cschempp/robotic-assembly-benchmark/static/images/board.png

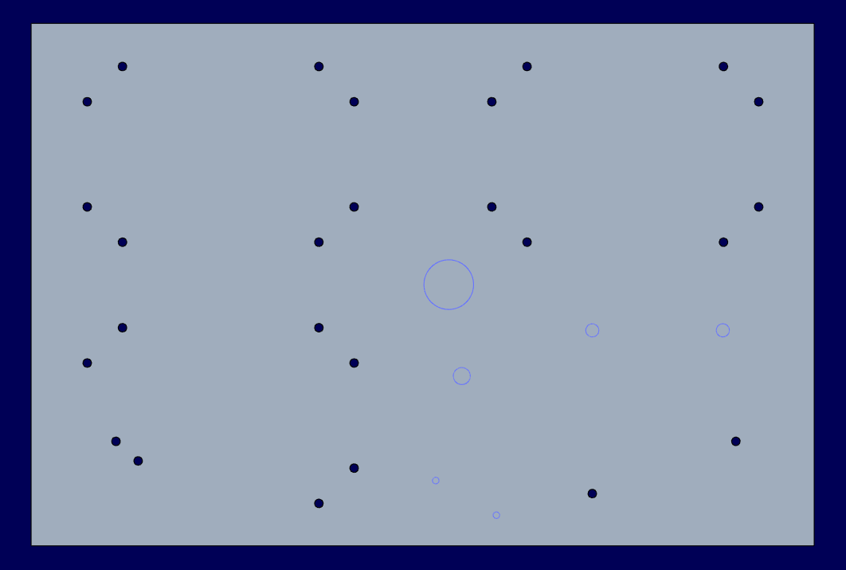
static/images/board.png
