cschempp/robotic-assembly-benchmark/static/images/bolt_midle_housing.png

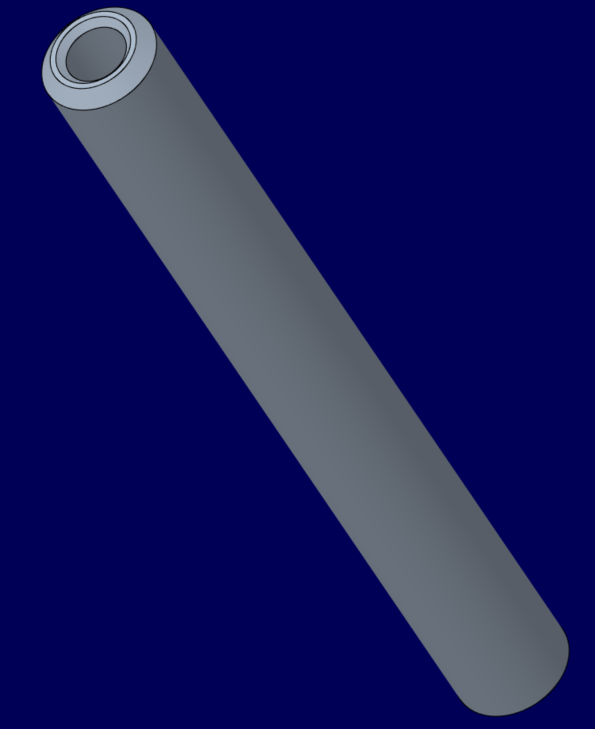
static/images/bolt_midle_housing.png
