cschempp/robotic-assembly-benchmark/static/images/clamp.png

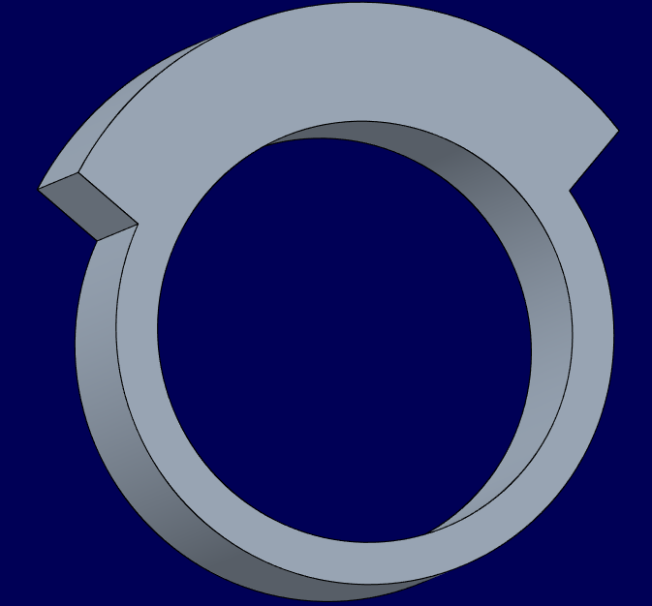
static/images/clamp.png
