cschempp/robotic-assembly-benchmark/static/images/coverplate.png

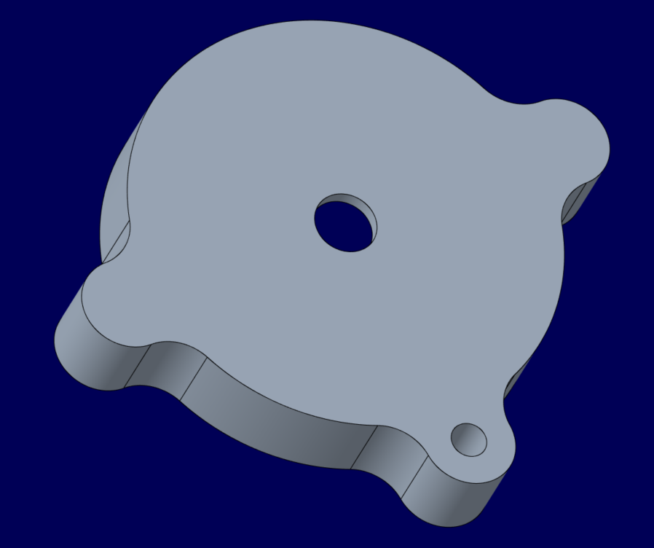
static/images/coverplate.png
