cschempp/robotic-assembly-benchmark/static/images/dowel_pin.png

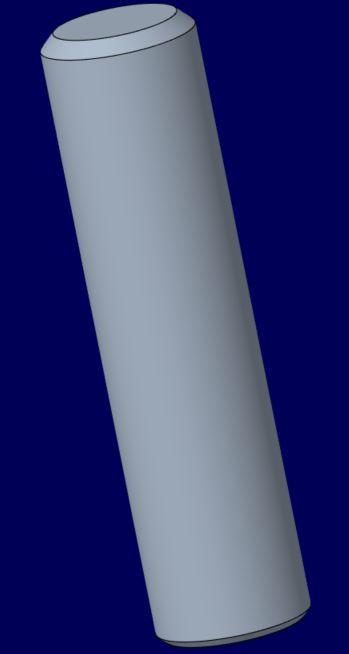
static/images/dowel_pin.png
