cschempp/robotic-assembly-benchmark/static/images/drawing_board.png

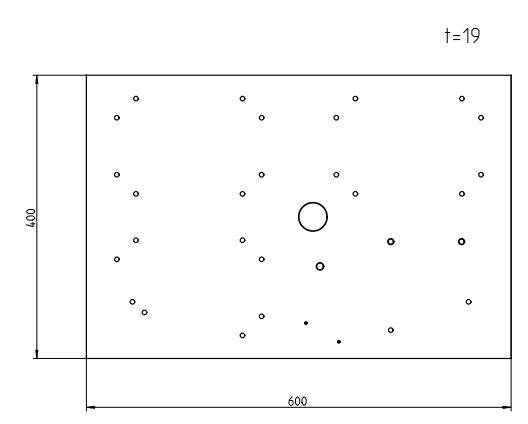
static/images/drawing_board.png
