cschempp/robotic-assembly-benchmark/static/images/fixation_0.png

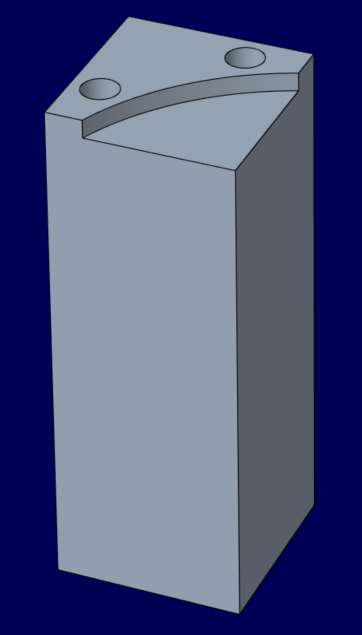
static/images/fixation_0.png
