cschempp/robotic-assembly-benchmark/static/images/fixation_1.png

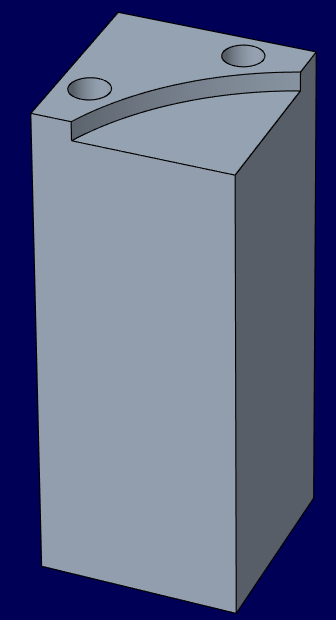
static/images/fixation_1.png
