cschempp/robotic-assembly-benchmark/static/images/fixation_2.png

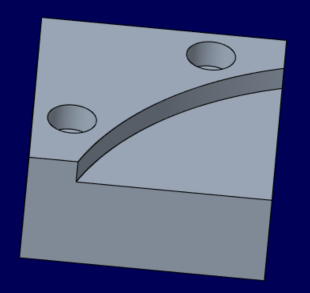
static/images/fixation_2.png
