cschempp/robotic-assembly-benchmark/static/images/fixation_3.png

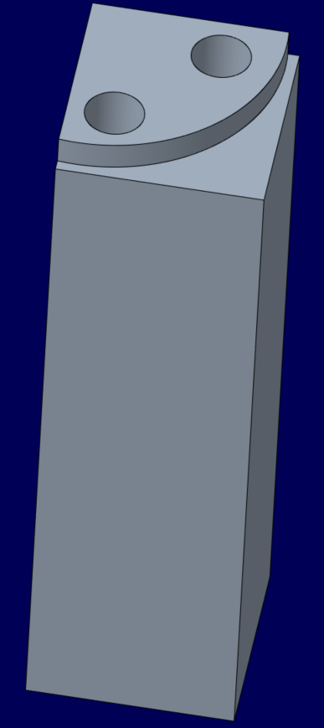
static/images/fixation_3.png
