cschempp/robotic-assembly-benchmark/static/images/gearwheel.png

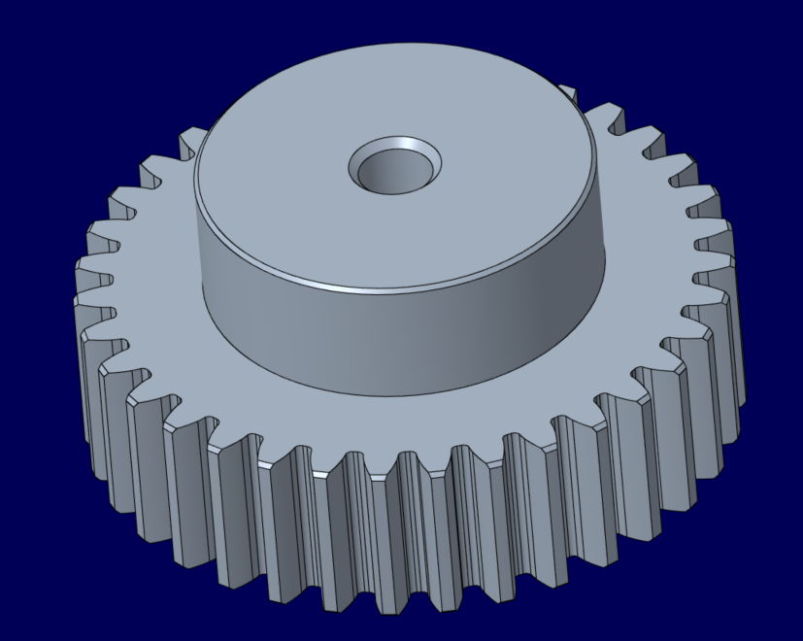
static/images/gearwheel.png
