cschempp/robotic-assembly-benchmark/static/images/housing_bottom.png

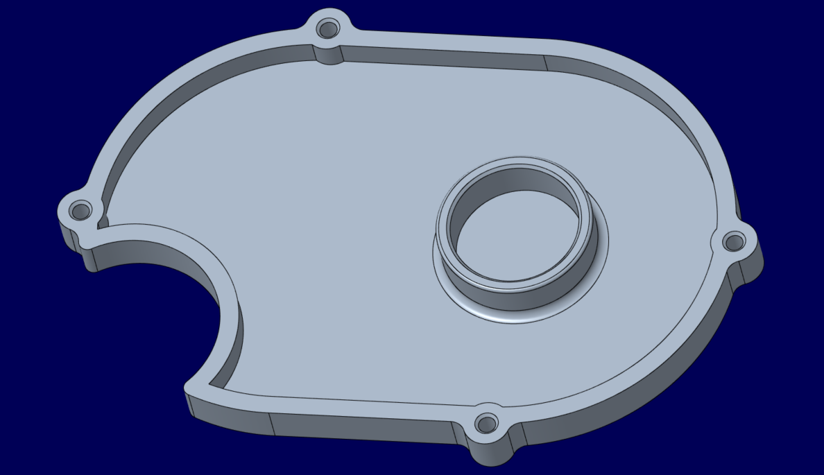
static/images/housing_bottom.png
