cschempp/robotic-assembly-benchmark/static/images/housing_center.png

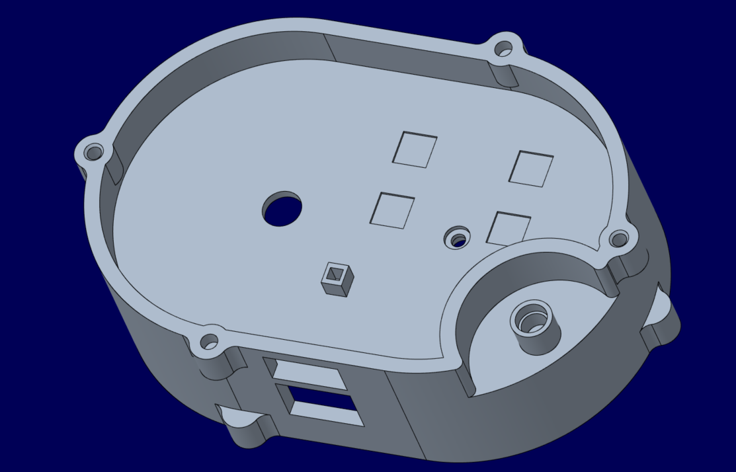
static/images/housing_center.png
