cschempp/robotic-assembly-benchmark/static/images/housing_top.png

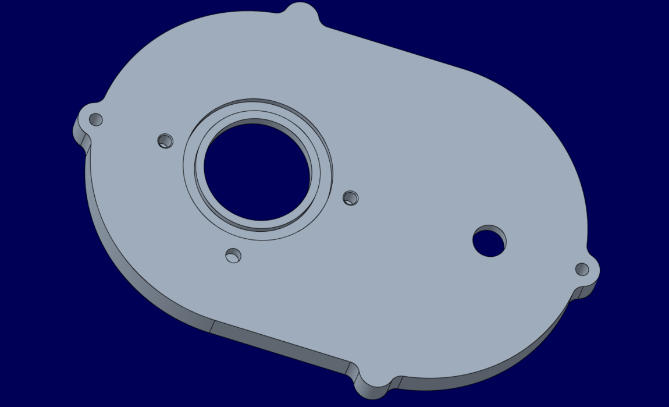
static/images/housing_top.png
