cschempp/robotic-assembly-benchmark/static/images/nozzle.png

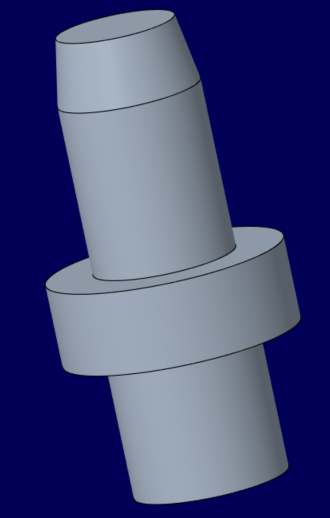
static/images/nozzle.png
