cschempp/robotic-assembly-benchmark/static/images/nut.png

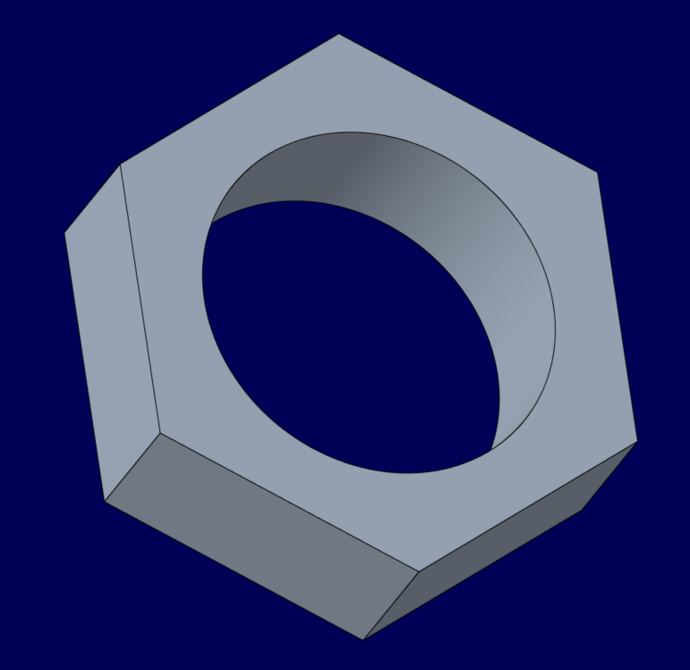
static/images/nut.png
