cschempp/robotic-assembly-benchmark/static/images/o_ring.png

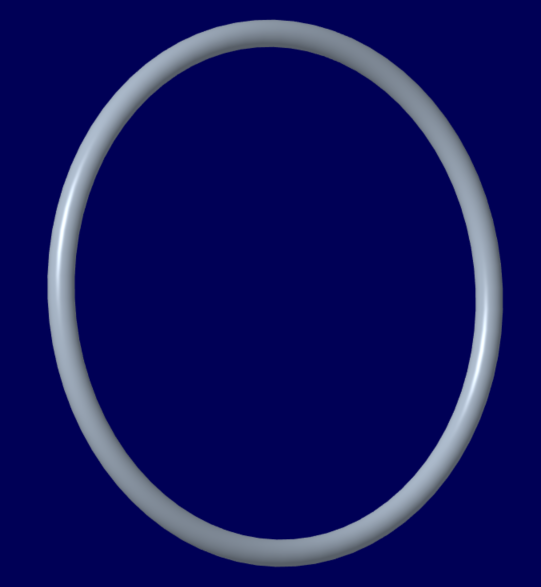
static/images/o_ring.png
