cschempp/robotic-assembly-benchmark/static/images/parallel_pins.jpg

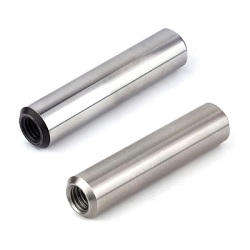
static/images/parallel_pins.jpg
