cschempp/robotic-assembly-benchmark/static/images/pcb.png

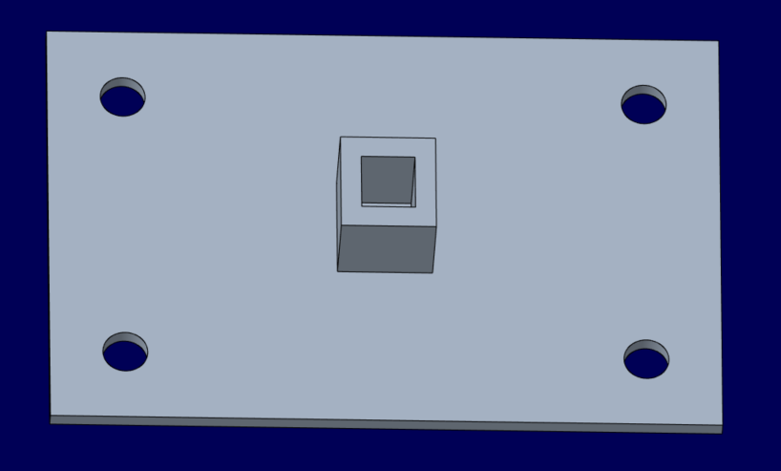
static/images/pcb.png
