cschempp/robotic-assembly-benchmark/static/images/pcb_pin.png

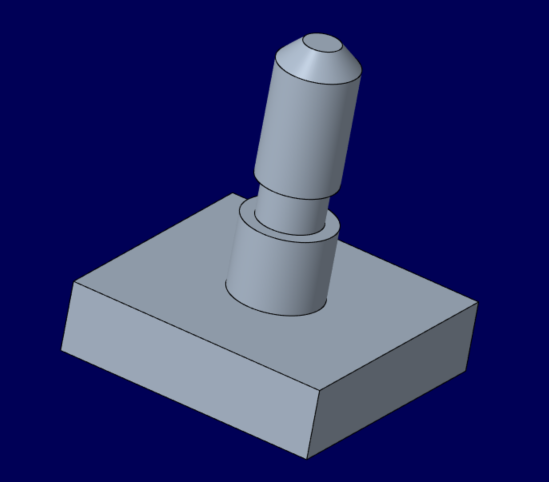
static/images/pcb_pin.png
