cschempp/robotic-assembly-benchmark/static/images/plug_inside_fixed.png

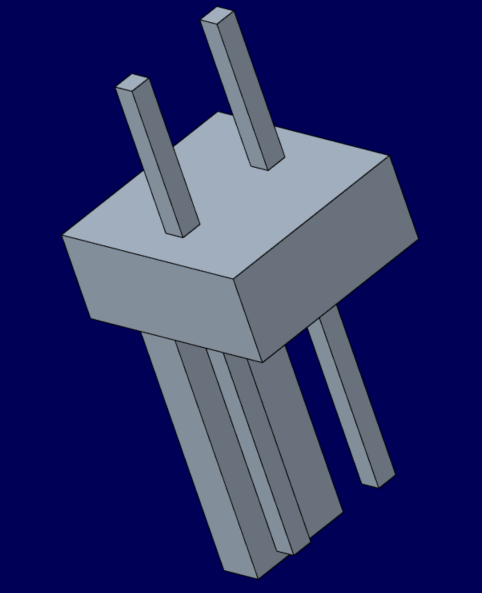
static/images/plug_inside_fixed.png
