cschempp/robotic-assembly-benchmark/static/images/plug_inside_loose.png

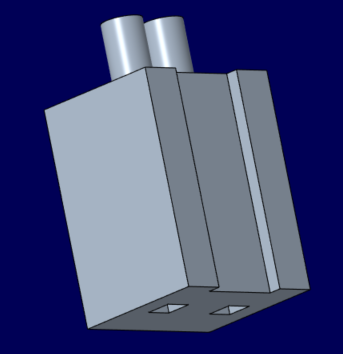
static/images/plug_inside_loose.png
