cschempp/robotic-assembly-benchmark/static/images/plug_outside_fixed.png

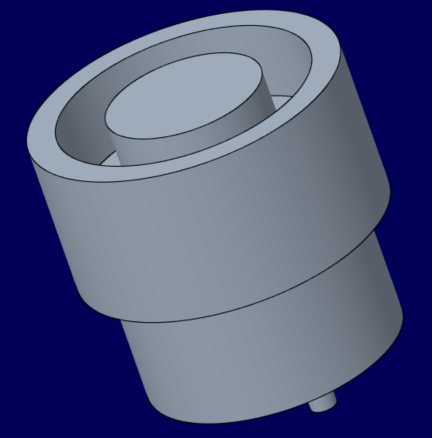
static/images/plug_outside_fixed.png
