cschempp/robotic-assembly-benchmark/static/images/plug_outside_loose.png

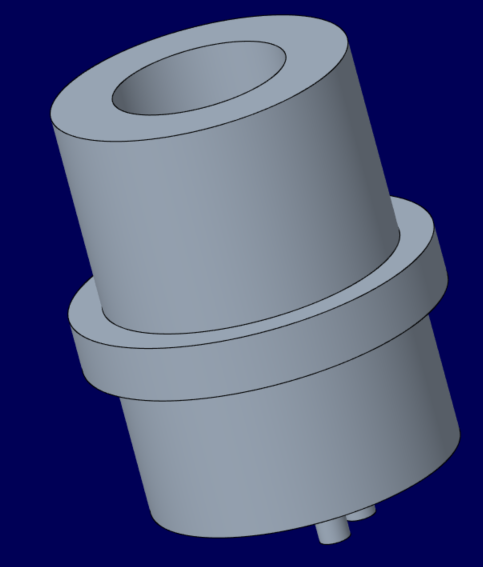
static/images/plug_outside_loose.png
