cschempp/robotic-assembly-benchmark/static/images/rerun_preview.png

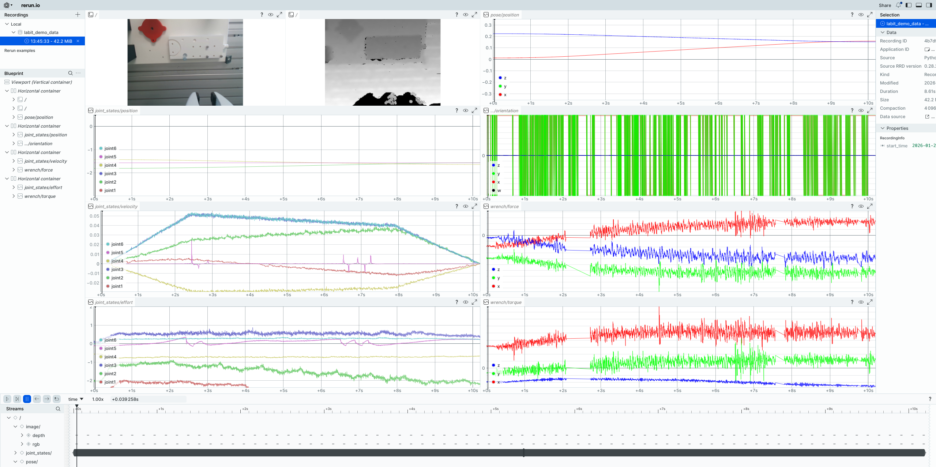
static/images/rerun_preview.png
