cschempp/robotic-assembly-benchmark/static/images/rotor.png

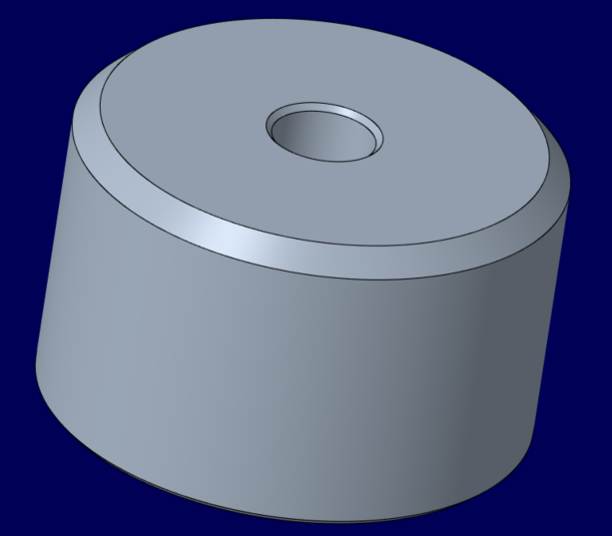
static/images/rotor.png
