cschempp/robotic-assembly-benchmark/static/images/screw_hexagon.png

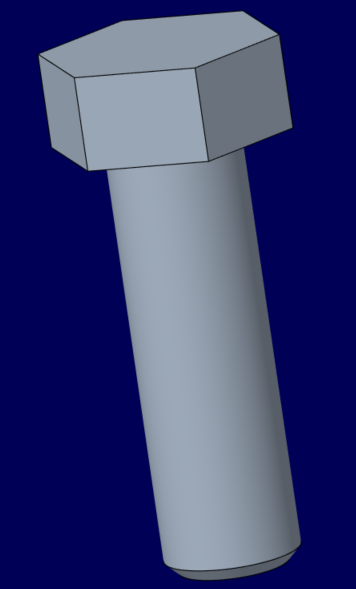
static/images/screw_hexagon.png
