cschempp/robotic-assembly-benchmark/static/images/screw_m5_12.png

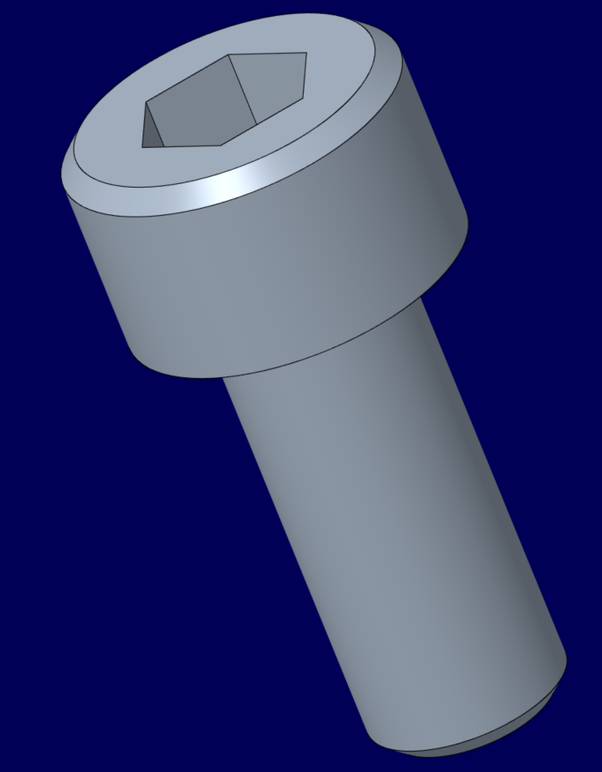
static/images/screw_m5_12.png
