cschempp/robotic-assembly-benchmark/static/images/tube.png

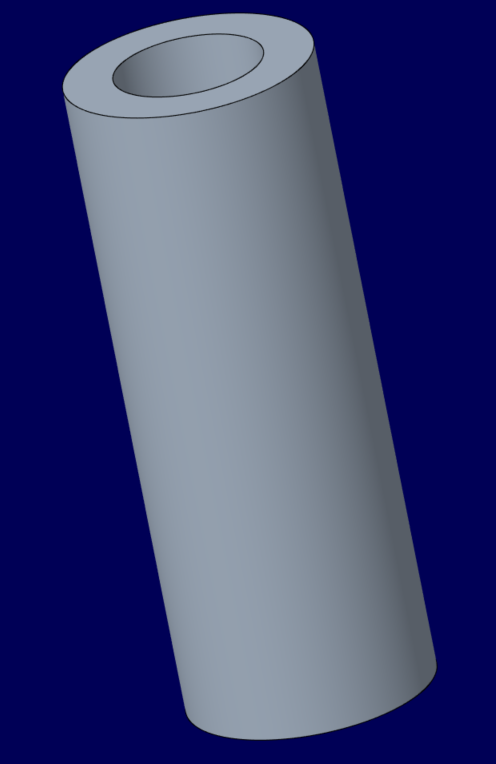
static/images/tube.png
