cschempp/robotic-assembly-benchmark/static/images/instructions_parts_list.jpg

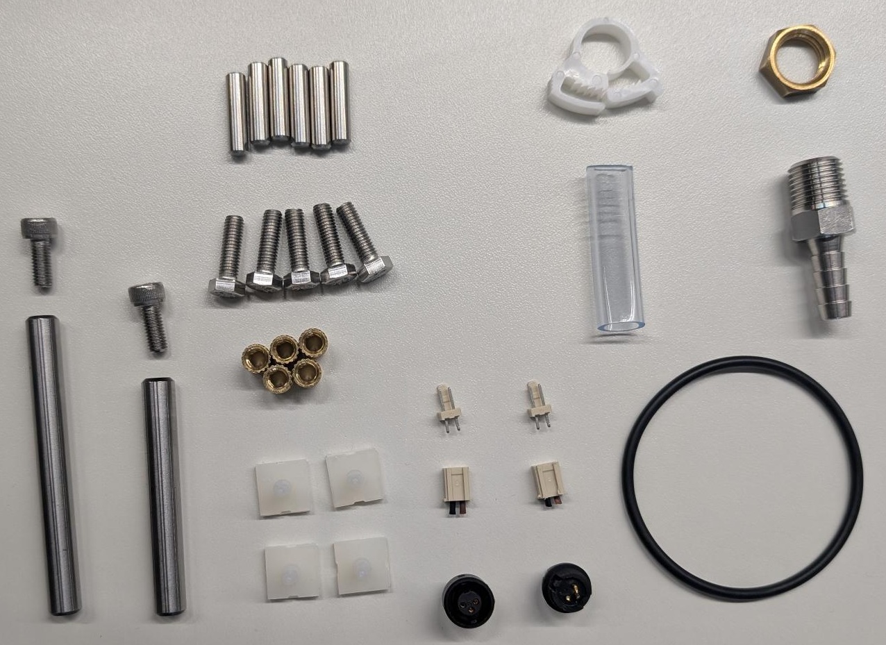
static/images/instructions_parts_list.jpg
