cschempp/robotic-assembly-benchmark/static/images/instructions_parts_positioning.jpg

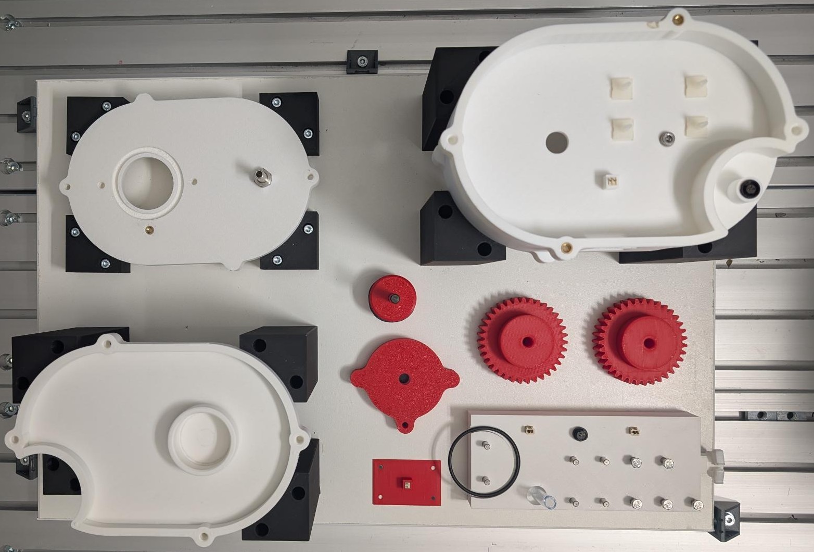
static/images/instructions_parts_positioning.jpg
