cschempp/robotic-assembly-benchmark/static/cad/cad_step/parts_supply.stp

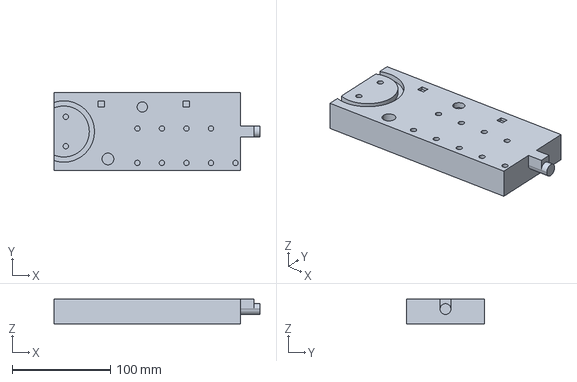
[picture p50: CAD file, 2025-04-22]
static/cad/cad_step/parts_supply.stp
210.0 x 80.0 x 25.0 mm
