cschempp/robotic-assembly-benchmark/static/cad/cad_step/threaded_insert_m5_length_5_8.stp

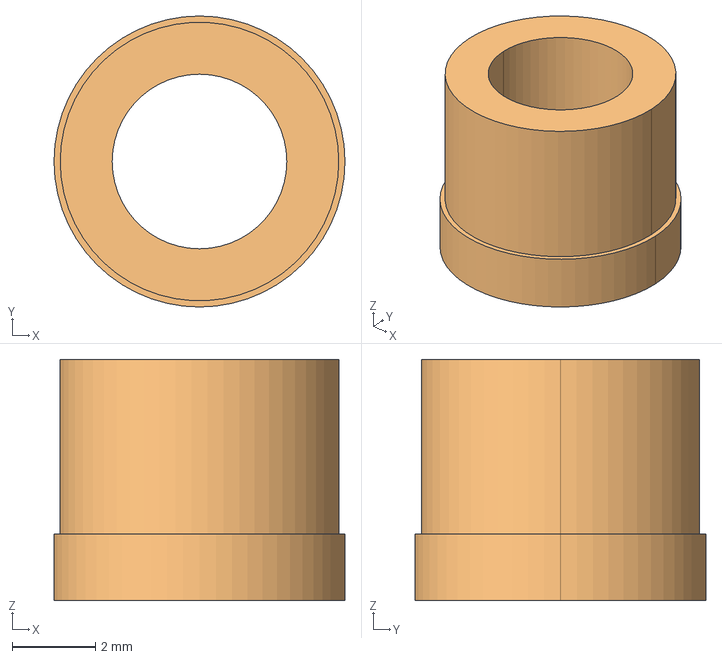
[picture p51: CAD file, 2025-04-22]
static/cad/cad_step/threaded_insert_m5_length_5_8.stp
7.00 x 7.00 x 5.80 mm
