cschempp/robotic-assembly-benchmark/static/cad/cad_step/pcb.stp

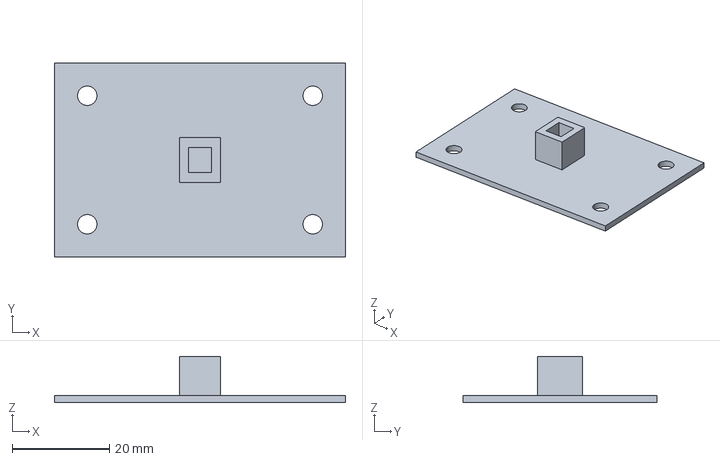
[picture p52: CAD file, 2025-04-22]
static/cad/cad_step/pcb.stp
60.0 x 40.0 x 9.50 mm
