cschempp/robotic-assembly-benchmark/static/cad/cad_step/rotor_printed_part.stp

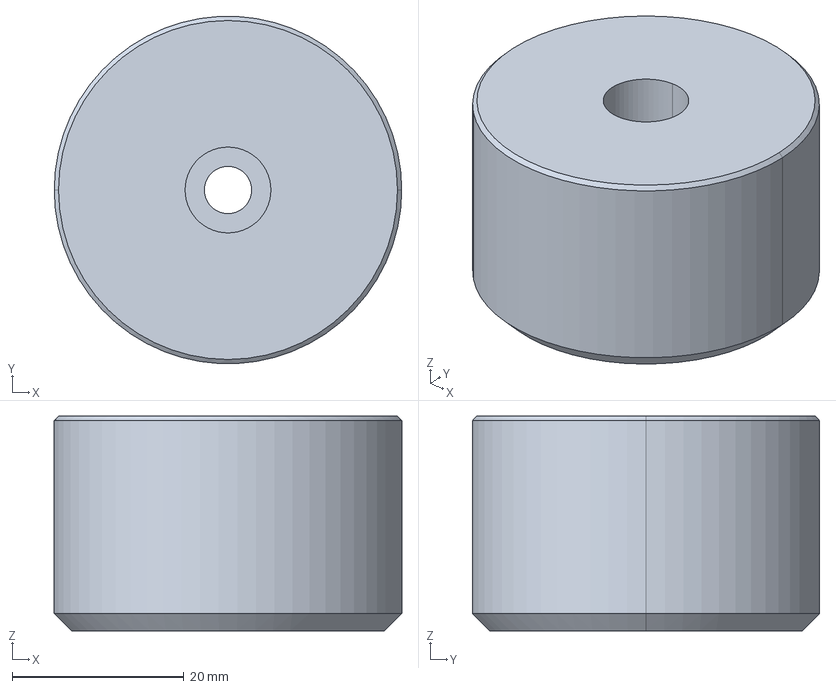
[picture p53: CAD file, 2025-04-22]
static/cad/cad_step/rotor_printed_part.stp
40.5 x 40.4 x 25.0 mm
