cschempp/robotic-assembly-benchmark/static/cad/cad_step/tube_clamp.stp

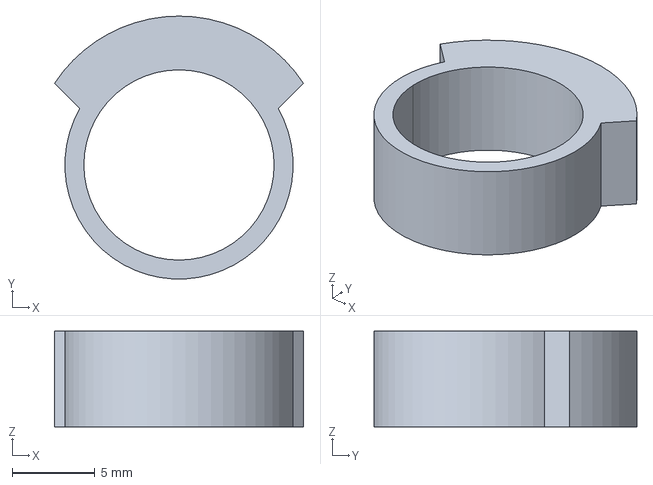
[picture p54: CAD file, 2025-04-22]
static/cad/cad_step/tube_clamp.stp
15.1 x 15.9 x 5.80 mm
