cschempp/robotic-assembly-benchmark/static/cad/cad_step/pin_pcb.stp

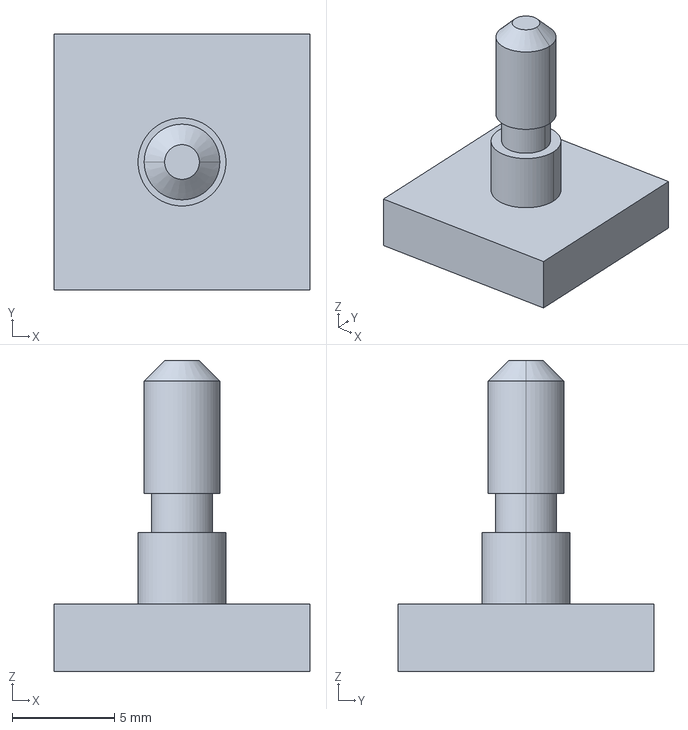
[picture p55: CAD file, 2025-04-22]
static/cad/cad_step/pin_pcb.stp
12.5 x 12.5 x 15.2 mm
