cschempp/robotic-assembly-benchmark/static/cad/cad_step/tube_nozzle.stp

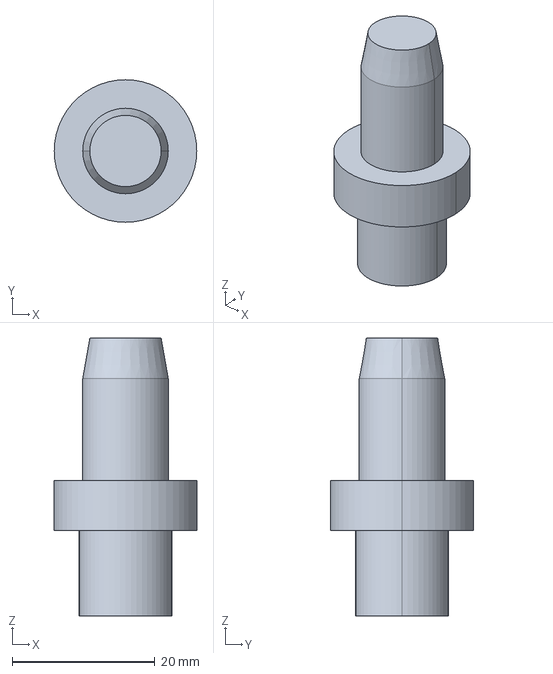
[picture p56: CAD file, 2025-04-22]
static/cad/cad_step/tube_nozzle.stp
20.0 x 20.0 x 39.0 mm
