cschempp/robotic-assembly-benchmark/static/cad/cad_step/plug_inside_fixed.stp

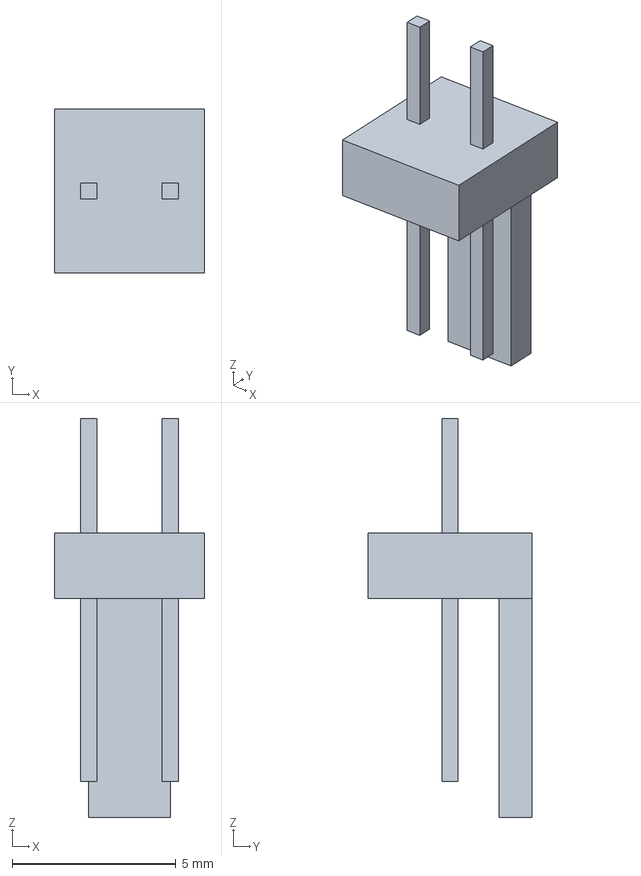
[picture p57: CAD file, 2025-04-22]
static/cad/cad_step/plug_inside_fixed.stp
4.60 x 5.00 x 12.2 mm
