cschempp/robotic-assembly-benchmark/static/cad/cad_step/gearwheel_teeth_35_mod_2.stp

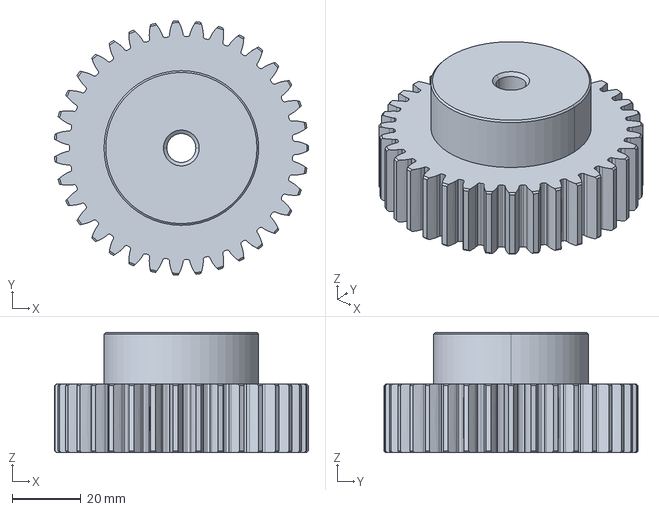
[picture p58: CAD file, 2025-04-22]
static/cad/cad_step/gearwheel_teeth_35_mod_2.stp
73.9 x 74.0 x 35.0 mm
