cschempp/robotic-assembly-benchmark/static/images/benchmark_assembly.png

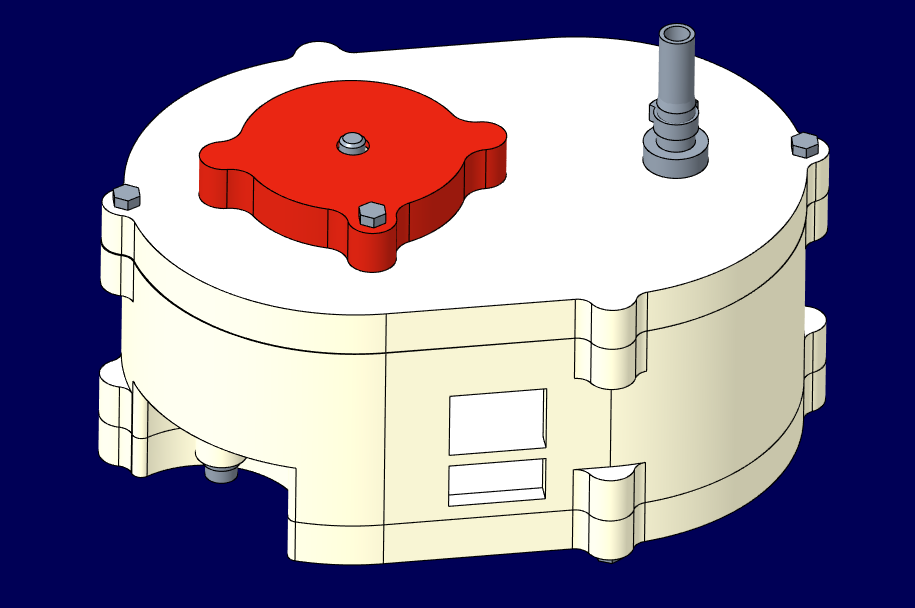
static/images/benchmark_assembly.png
