cschempp/robotic-assembly-benchmark/static/images/housing_bottom_assembly.png

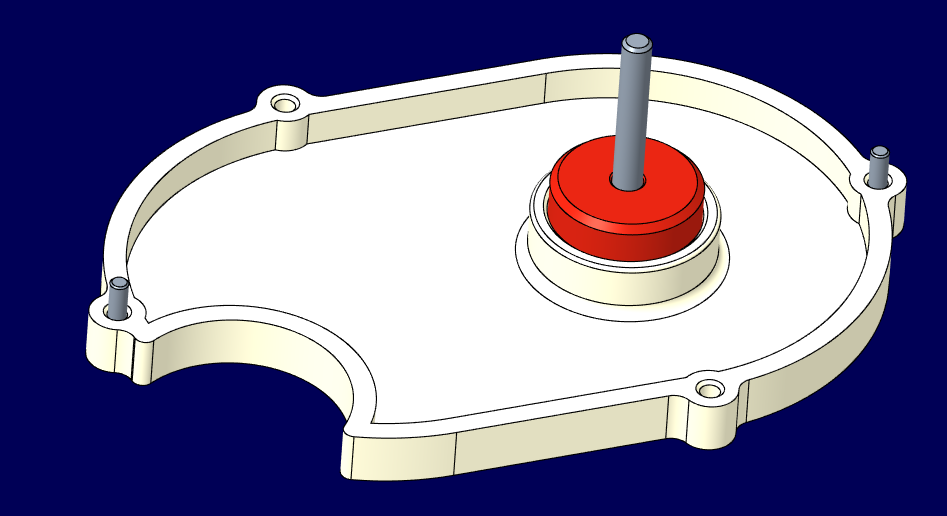
static/images/housing_bottom_assembly.png
