cschempp/robotic-assembly-benchmark/static/images/housing_middle_assembly_initial.png

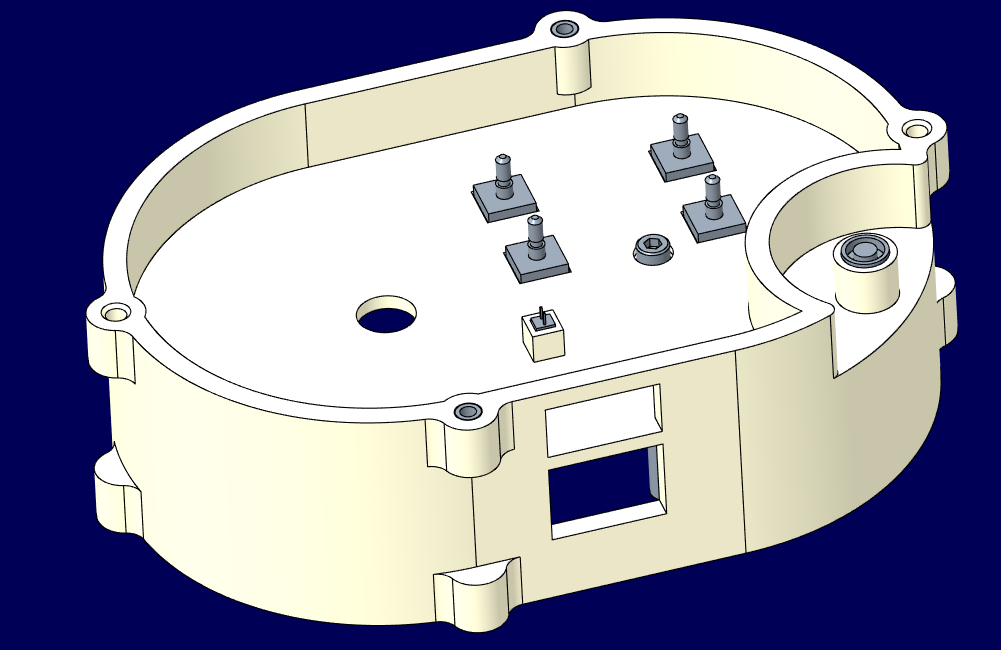
static/images/housing_middle_assembly_initial.png
