cschempp/robotic-assembly-benchmark/static/images/housing_top_assembly.png

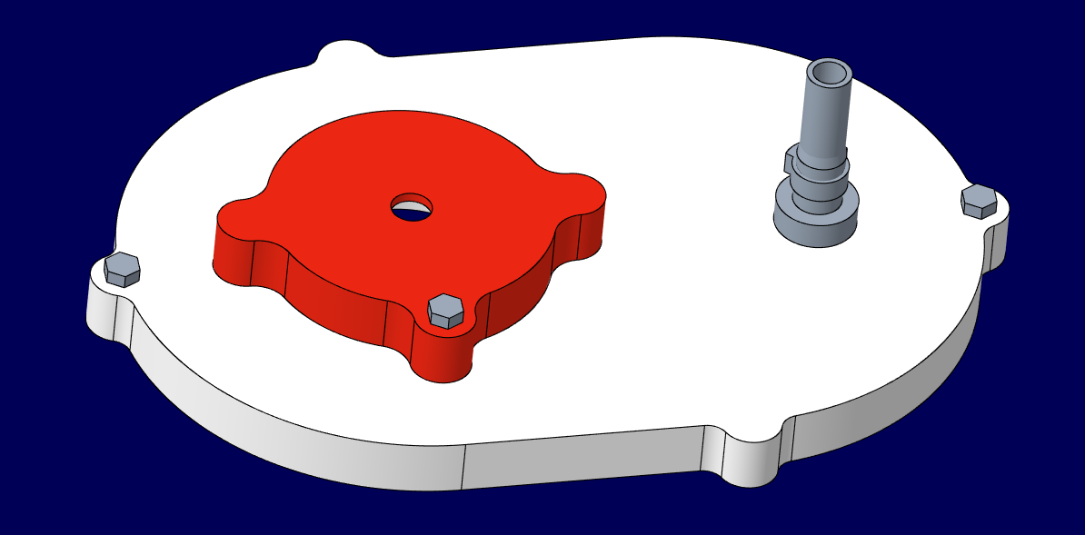
static/images/housing_top_assembly.png
