cschempp/robotic-assembly-benchmark/static/images/housing_top_assembly_initial.png

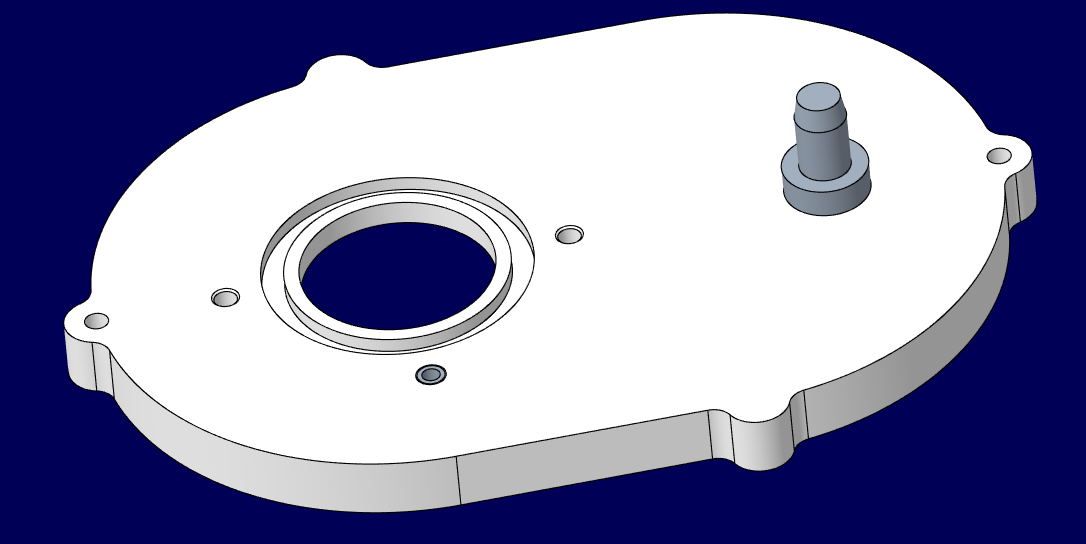
static/images/housing_top_assembly_initial.png
