cschempp/robotic-assembly-benchmark/static/images/instructions_board_0.png

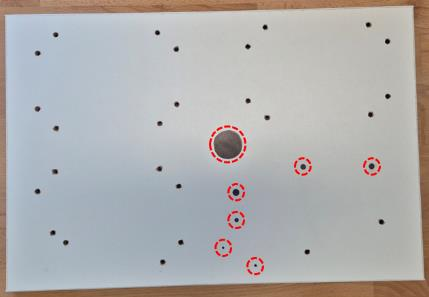
static/images/instructions_board_0.png
