cschempp/robotic-assembly-benchmark/static/images/instructions_board_2.png

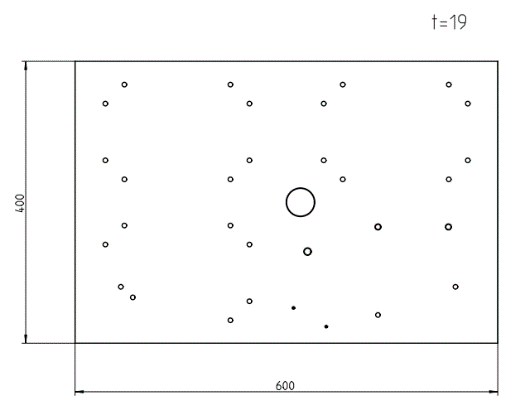
static/images/instructions_board_2.png
