cschempp/robotic-assembly-benchmark/static/images/instructions_board_3.png

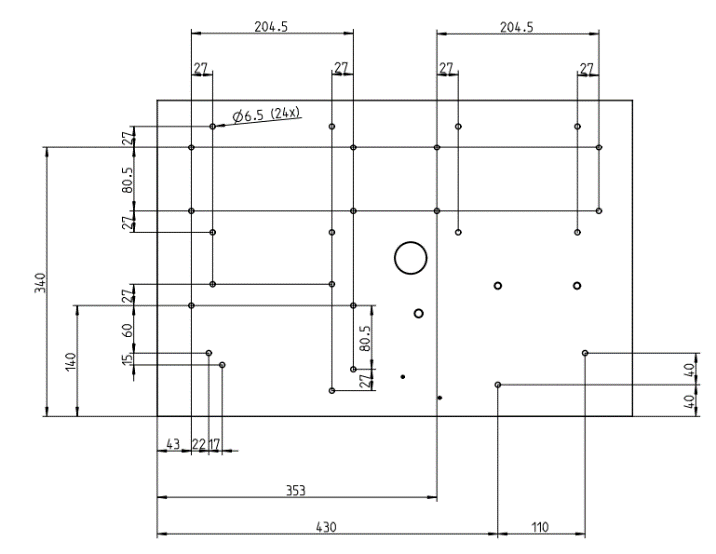
static/images/instructions_board_3.png
