cschempp/robotic-assembly-benchmark/static/images/instructions_board_4.png

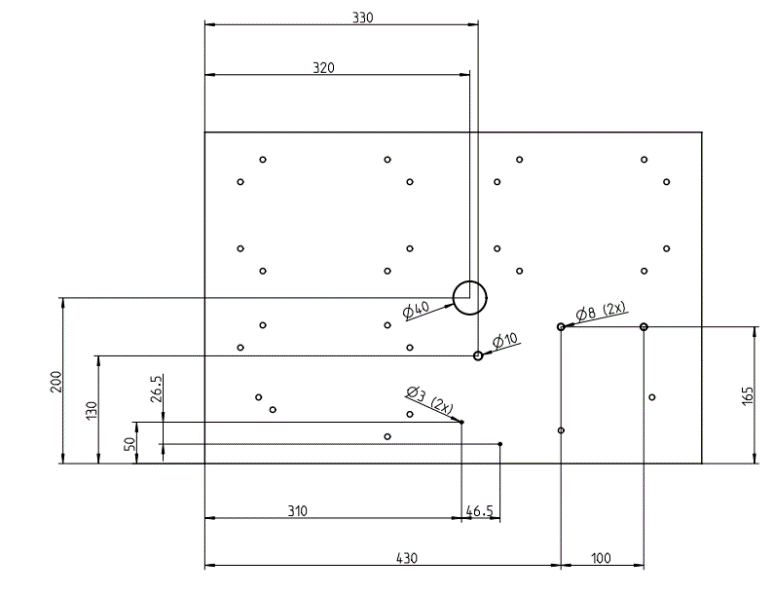
static/images/instructions_board_4.png
