cschempp/robotic-assembly-benchmark/static/images/instructions_fixed_plug_inside.jpg

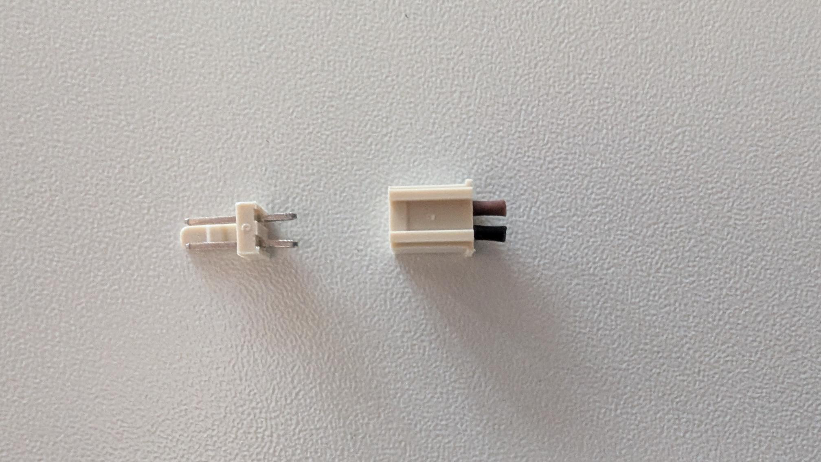
static/images/instructions_fixed_plug_inside.jpg
