cschempp/robotic-assembly-benchmark/static/images/instructions_housing_middle_topview.jpg

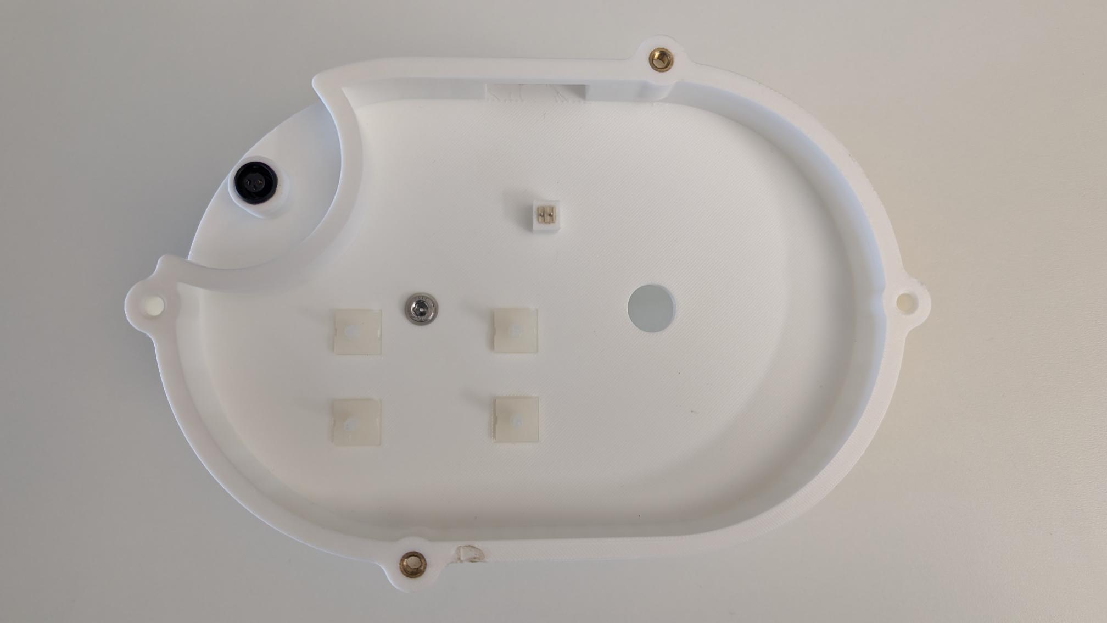
static/images/instructions_housing_middle_topview.jpg
