cschempp/robotic-assembly-benchmark/static/images/instructions_housing_top.jpg

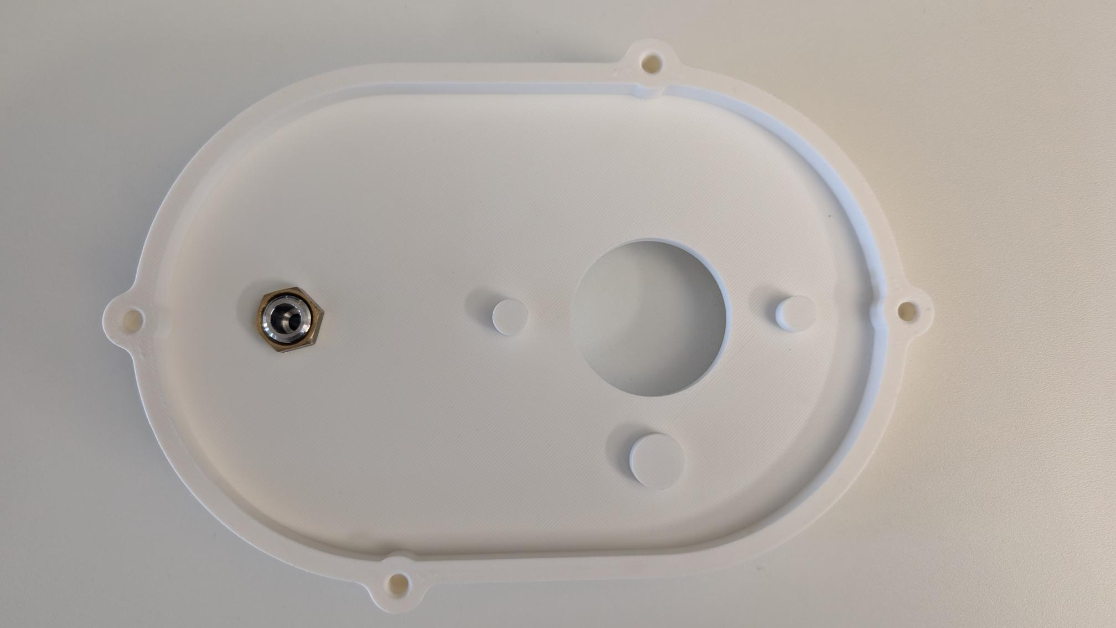
static/images/instructions_housing_top.jpg
