cschempp/robotic-assembly-benchmark/static/images/instructions_pcb.png

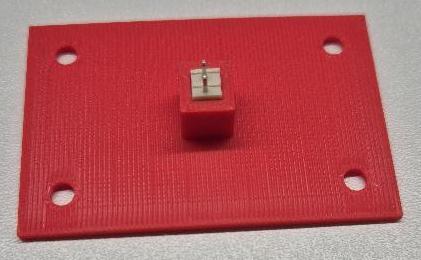
static/images/instructions_pcb.png
