cschempp/robotic-assembly-benchmark/static/images/instructions_pcb_pins.png

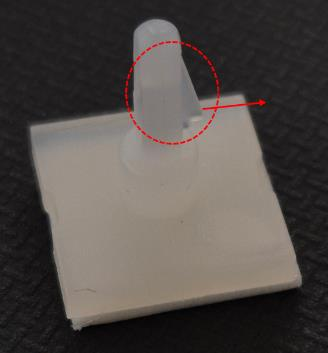
static/images/instructions_pcb_pins.png
