cschempp/robotic-assembly-benchmark/static/images/instructions_plug_outside.png

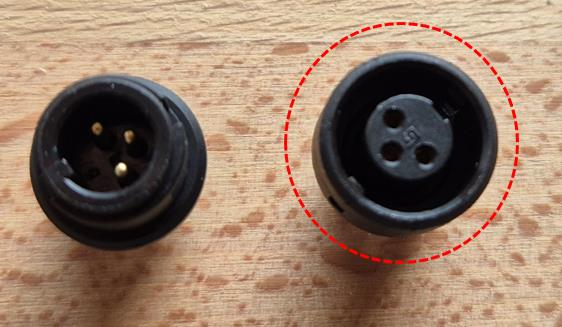
static/images/instructions_plug_outside.png
