cschempp/robotic-assembly-benchmark/static/images/instructions_plugs_inside.jpg

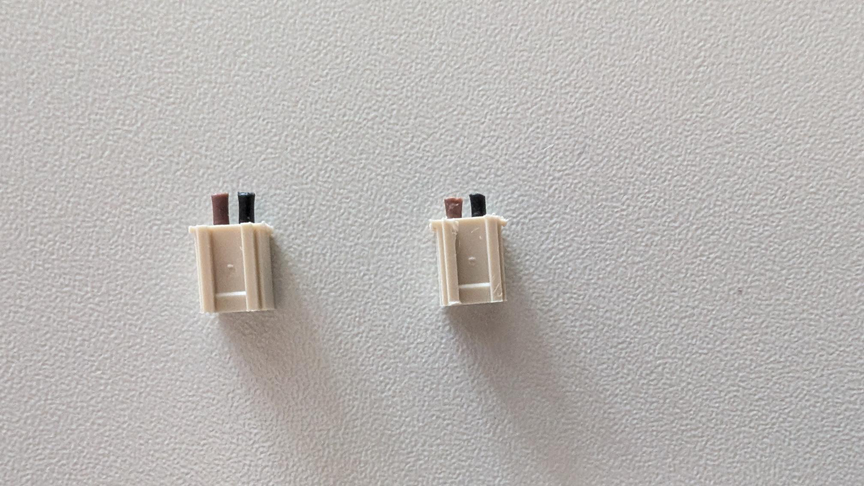
static/images/instructions_plugs_inside.jpg
