cschempp/robotic-assembly-benchmark/static/images/instructions_rotor.png

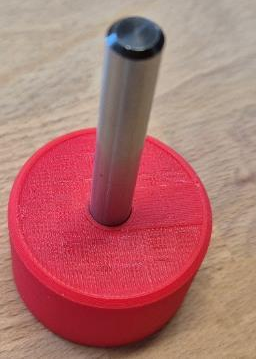
static/images/instructions_rotor.png
