cschempp/robotic-assembly-benchmark/static/images/instructions_tube.jpg

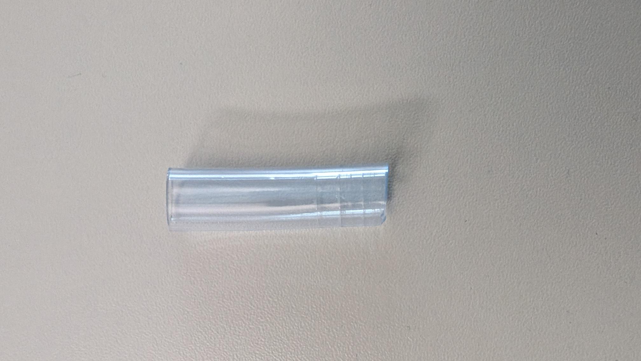
static/images/instructions_tube.jpg
