cschempp/robotic-assembly-benchmark/static/images/rotor_assembly.png

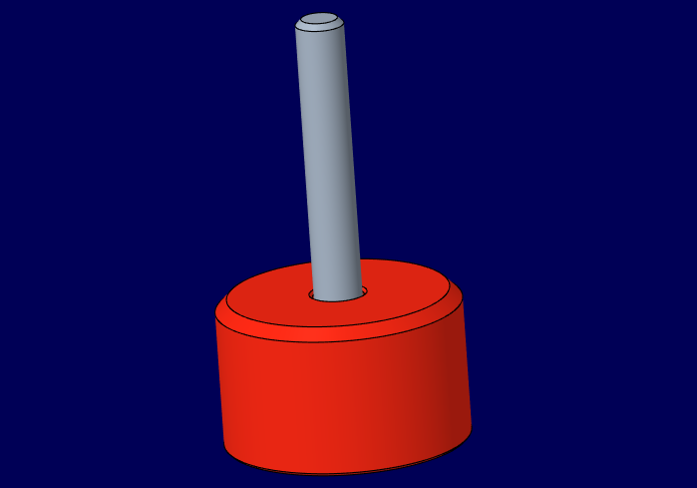
static/images/rotor_assembly.png
