cschempp/robotic-assembly-benchmark/static/images/benchmark_final_position.png

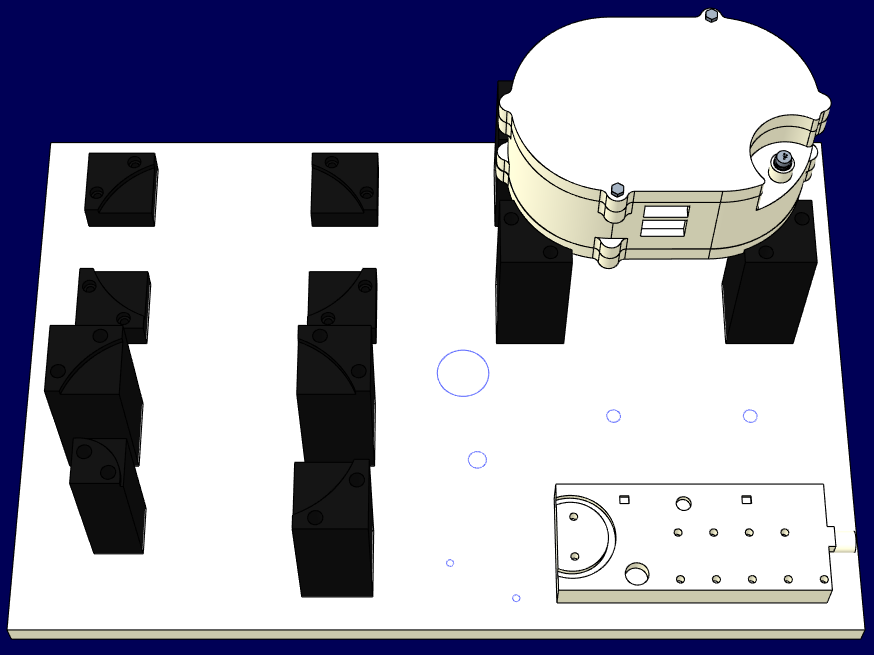
static/images/benchmark_final_position.png
