cschempp/robotic-assembly-benchmark/static/images/benchmark_initial_position.png

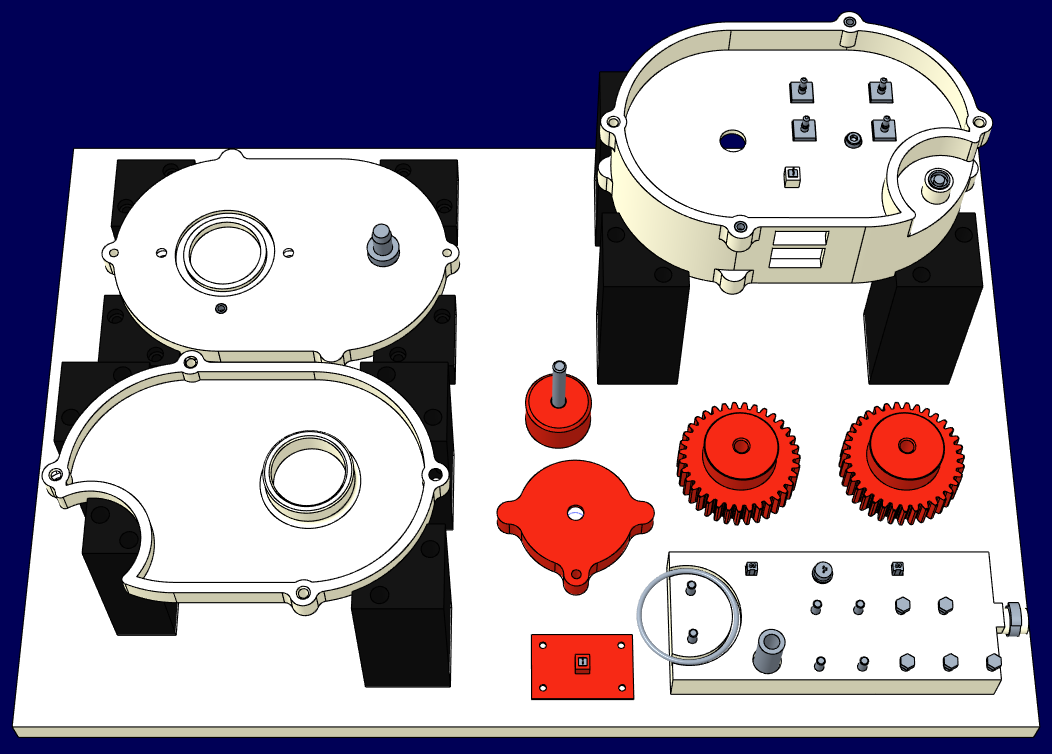
static/images/benchmark_initial_position.png
