cschempp/robotic-assembly-benchmark/static/images/evaluation_template.png

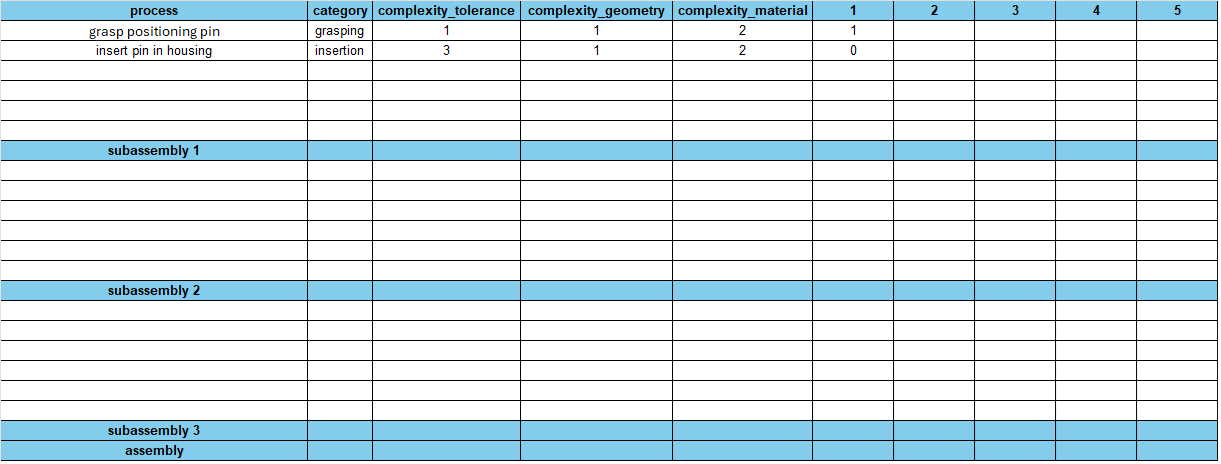
static/images/evaluation_template.png
